tobyp/kthw/schematics/kthw_memory.sch

## KiCad design schematics/kthw_memory.sch (2019-12-05)

Schematic: kthw_memory.sch

Parts:
AFF5, AFF6, AFF7, AFF8, AFF9: LTS-6980HR
D43, D44, D45, D46, D47, D52: LED
D48, D49, D50, D51: 1N4148; D_DO-35_SOD27_Horizontal_RM10
R58, R59, R60, R61, R62, R63, R64, R65, R66, R67, R68, R69, R70, R71, R72, R73, R74, R75, R76, R77, R78, R79, R80, R81, R82, R83, R84, R85, R86, R87, R88, R89, R90, R91, R92, R93, R94, R95, R96, R97, R98, R99, R100, R101, R102, R103: 1K
SW13, SW14, SW15, SW16: SW_Push
U12, U13, U14, U15, U16, U17, U18: 74HC595
