tobyp/kthw/schematics/kthw_morse.sch

## KiCad design schematics/kthw_morse.sch (2019-12-05)

Schematic: kthw_morse.sch

Parts:
AFF1, AFF2, AFF3, AFF4: LTS-6980HR
D32, D33: LED
R19, R20, R21, R22, R23, R24, R25, R26, R27, R28, R29, R30, R31, R32, R33, R34, R35, R36, R37, R38, R39, R40, R41, R42, R43, R44, R45, R46, R47, R48, R49, R50, R51, R52: 1K
RV2: POT
SW8: SW_Push
U7, U8, U9, U10: 74HC595
