tobyp/kthw/schematics/kthw_password.sch

## KiCad design schematics/kthw_password.sch (2019-12-05)

Schematic: kthw_password.sch

Parts:
D1, D2, D3, D4, D5: 1N4148; D_DO-35_SOD27_Horizontal_RM10
D6: LED
DS1: LCD16X2; WC1602A
R1: 1K
RV1: 100K
SW2, SW3, SW4, SW5, SW6: SW_Push
U2, U3: 74HC595
