tobyp/kthw/schematics/kthw_schematics.sch

## KiCad design schematics/kthw_schematics.sch (2019-12-05)

Schematic: kthw_schematics.sch

Parts:
J1, J2: CONN_02X25
SW1: SW_SPST
U1: 7805
