tobyp/kthw/schematics/kthw_simonsays.sch

## KiCad design schematics/kthw_simonsays.sch (2019-12-05)

Schematic: kthw_simonsays.sch

Parts:
D34, D36, D38, D40: 1N4148; D_DO-35_SOD27_Horizontal_RM10
D35: LED_YL
D37: LED_RD
D39: LED_BL
D41: LED_GR
D42: LED
R53, R54, R55, R56, R57: 1K
SW9, SW10, SW11, SW12: SW_Push
U11: 74HC595
