tobyp/kthw/schematics/kthw_timer.sch

## KiCad design schematics/kthw_timer.sch (2019-12-05)

Schematic: kthw_timer.sch

Parts:
AFF10, AFF11, AFF12, AFF13: LTS-6980HR
D53, D54, D55: LED
D56, D57, D58, D59, D60, D61, D62, D63, D64, D65, D66, D67, D68, D69, D70, D71: 1N4148; D_DO-35_SOD27_Horizontal_RM10
J5: CONN_01X04
R104, R105, R106, R107, R108, R109, R110, R111, R112, R113, R114, R115, R116, R117, R118, R119, R120, R121, R122, R123, R124, R125, R126, R127, R128, R129, R130, R131, R132, R133, R134, R135, R136, R137, R138: 1K
SW17, SW18: SW_DIP_x08
U19, U20, U21, U22, U23, U24, U25: 74HC595
