tobyp/kthw/schematics/kthw_wires.sch

## KiCad design schematics/kthw_wires.sch (2019-12-05)

Schematic: kthw_wires.sch

Parts:
D7, D8, D9, D10, D11, D12, D13, D14: 1N4148; D_DO-35_SOD27_Horizontal_RM10
D15, D16, D17, D18, D19, D20, D21, D22, D23, D24, D25, D26, D27, D28, D29, D30, D31: LED
J3, J4: CONN_01X15
R2, R3, R4, R5, R6, R7, R8, R9, R10, R11, R12, R13, R14, R15, R16, R17, R18: 1K
SW7: SW_Push
U4, U5, U6: 74HC595
