tobyp/kthw/password.c

/* KTHW - Hardware Clone of Keep Talking and Nobody Explodes
Copyright (C) 2017 Toby P., Thomas H.
Copyright (C) 2019 Toby P.

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
You should have received a copy of the GNU General Public License
along with this program.  If not, see <http://www.gnu.org/licenses/>. */

#include "password.h"

#include <stdlib.h>

/* The password module has 5 cylinder columns of 6 letters each, which can be
spun to spell exactly one word from the a pre-defined list. To disable the
module, you must find that exact word, select it, and press the submit
button. */

struct word {
	char chars[6];
};

// impossibles[N] == the letters that can never appear in column N.
struct slot_impossible {
	unsigned char count;
	char letters[25];  // if all 26 were impossible, the puzzle would be unsolvable!
};

#include "password.words.generated.c"

#define BTN_RIGHT 0x1
#define BTN_LEFT 0x2
#define BTN_DOWN 0x4
#define BTN_UP 0x8
#define BTN_SUBMIT 0x10

static void populate_cylinders(struct password * password) {
	/* possibilities[word] tracks whether that word is possible, per column, as a bitmask.
	E.g. 0x1f means it is possible in every column and thus totally possible. */
	uint8_t possibilities[sizeof(words)/sizeof(struct word)];
	for (uint8_t i=0; i<sizeof(possibilities); ++i) {
		possibilities[i] = 0;
	}

	password->letters[0][0] = password->word->chars[0];
	password->letters[1][0] = password->word->chars[1];
	password->letters[2][0] = password->word->chars[2];
	password->letters[3][0] = password->word->chars[3];
	password->letters[4][0] = password->word->chars[4];

	uint32_t has_letter[5] = {
		1 << (password->letters[0][0] - 'A'),
		1 << (password->letters[1][0] - 'A'),
		1 << (password->letters[2][0] - 'A'),
		1 << (password->letters[3][0] - 'A'),
		1 << (password->letters[4][0] - 'A'),
	};

	for (uint8_t col=0; col<5; ++col) {
		for (uint8_t row=0; row<6; ++row) {
			if (row != 0) {  // row 0 already contains the password letter, don't change that
				/* generate a new letter for that column. */
				uint8_t letter = rnd_range(0, 26);
				while (has_letter[col] & (1 << letter)) {
					letter = (letter + 1) % 26;
				}
				password->letters[col][row] = letter + 'A';
				has_letter[col] |= (1 << letter);
			}
			for (uint8_t word=0; word<sizeof(possibilities); ++word) {
				if (words[word].chars[col] == password->letters[col][row]) {
					possibilities[word] |= (1 << col);
				}
			}
		}
	}

	for (uint8_t word=0; word<sizeof(possibilities); ++word) {
		if (&words[word] == password->word) continue;  // don't touch the password
		if (possibilities[word] == 0x1f) { //this word is possible but shouldn't be -- block it!
			/* select a random column to block the word on. */
			uint8_t col = rnd_range(0, 5);
			while (password->word->chars[col] == words[word].chars[col]) { //do not change a row where password == blockword
				col = (col + 1) % 5;
			}
			/* find the letter that makes the word possible */
			uint8_t row = 0;
			while (words[word].chars[col] != password->letters[col][row]) {
				++row;
			}
			/* Chose a replacement that never appears in that column, but also isn't a duplicate */
			uint8_t replacement = rnd_range(0, impossibles[col].count);
			while (has_letter[col] & (1 << impossibles[col].letters[replacement])) {
				replacement = (replacement + 1) % impossibles[col].count;
			}

			password->letters[col][row] = impossibles[col].letters[replacement];
		}
	}
}

void password_prepare_tick(struct bomb * bomb, struct module * module) {
	struct password * password = (struct password *)module;
	switch (password->ticks) {
	//init
	case 0:
		password->word = &words[rnd_range(0, sizeof(words)/sizeof(struct word))];
		printf("[%s] word=\"%s\"\n", module->name, password->word->chars);

		populate_cylinders(password);

		/* "Spin" the cylinders. Are you feeling lucky, punk? */
		password->selections[0] = rnd_range(0, 6);
		password->selections[1] = rnd_range(0, 6);
		password->selections[2] = rnd_range(0, 6);
		password->selections[3] = rnd_range(0, 6);
		password->selections[4] = rnd_range(0, 6);

		password->lcd->mode = LCD_CMD;
		password->lcd->cmd = 0x0c;
		break;
	case 1:
		password->lcd->mode = LCD_CMD;
		password->lcd->cmd = 0x38;
		break;
	case 2:
		password->lcd->mode = LCD_CMD;
		password->lcd->cmd = 0x06;
		break;
	case 3:
		password->lcd->mode = LCD_CMD;
		password->lcd->cmd = 0x01;
		break;
	//password
	case 4:
		password->lcd->mode = LCD_CMD;
		password->lcd->cmd = LCD_CMD_CURSOR(0, 1);
		break;
	case 5:
		password->lcd->mode = LCD_DATA;
		password->lcd->cmd = password->letters[0][password->selections[0]];
		break;
	case 6:
		password->lcd->mode = LCD_CMD;
		password->lcd->cmd = LCD_CMD_CURSOR(0, 4);
		break;
	case 7:
		password->lcd->mode = LCD_DATA;
		password->lcd->cmd = password->letters[1][password->selections[1]];
		break;
	case 8:
		password->lcd->mode = LCD_CMD;
		password->lcd->cmd = LCD_CMD_CURSOR(0, 7);
		break;
	case 9:
		password->lcd->mode = LCD_DATA;
		password->lcd->cmd = password->letters[2][password->selections[2]];
		break;
	case 10:
		password->lcd->mode = LCD_CMD;
		password->lcd->cmd = LCD_CMD_CURSOR(0, 10);
		break;
	case 11:
		password->lcd->mode = LCD_DATA;
		password->lcd->cmd = password->letters[3][password->selections[3]];
		break;
	case 12:
		password->lcd->mode = LCD_CMD;
		password->lcd->cmd = LCD_CMD_CURSOR(0, 13);
		break;
	case 13:
		password->lcd->mode = LCD_DATA;
		password->lcd->cmd = password->letters[4][password->selections[4]];
		break;
	case 14:
		password->lcd->mode = LCD_CMD;
		password->lcd->cmd = LCD_CMD_CURSOR(1, 1);
		break;
	case 15:
		password->lcd->mode = LCD_DATA;
		password->lcd->cmd = '^';
		break;
	default:
		password->ticks = 0;
		password->ser->value = 1;
		module->flags |= MF_READY;
		return;
	}
	password->ticks++;
}

void password_tick(struct bomb * bomb, struct module * module) {
	struct password * password = (struct password *)module;
	uint8_t pos = password->pos;
	uint8_t sel = password->selections[pos];

	uint32_t button_index = password->ticks;
	uint8_t button_mask = 1 << button_index;
	uint8_t button_value = gpio_get(password->in) ? button_mask : 0;
	if ((password->cache & button_mask) != button_value) {
		password->cache = (password->cache & ~button_mask) | button_value;
		if (button_value) {
			if (button_value == BTN_LEFT) {
				if (password->pos > 0) password->pos--;
			}
			else if (button_value == BTN_RIGHT) {
				if (password->pos < 4) password->pos++;
			}
			else if (button_value == BTN_UP) {
				sel = (sel + 5) % 6; //equivalent to -1 without the underflow (which should be harmless but makes me queasy)
			}
			else if (button_value == BTN_DOWN) {
				sel = (sel + 1) % 6;
			}
			else if (button_value == BTN_SUBMIT) {
				for (uint8_t i=0; i<6; ++i) {
					if (password->letters[i][password->selections[i]] != password->word->chars[i]) {
						strike(bomb, module);
						return;
					}
				}
				module->flags |= MF_COMPLETE;
				return;
			}
		}
	}

	if (password->pos != pos) {
		sel = password->selections[pos];
		password->lcd_cache[0].mode = LCD_CMD;
		password->lcd_cache[0].cmd = LCD_CMD_CURSOR(1, 1 + 3*pos);
		password->lcd_cache[1].mode = LCD_DATA;
		password->lcd_cache[1].cmd = ' ';
		password->lcd_cache[2].mode = LCD_CMD;
		password->lcd_cache[2].cmd = LCD_CMD_CURSOR(1, 1 + 3*password->pos);
		password->lcd_cache[3].mode = LCD_DATA;
		password->lcd_cache[3].cmd = '^';
	}

	if (password->selections[pos] != sel) {
		password->selections[pos] = sel;
		password->lcd_cache[4].mode = LCD_CMD;
		password->lcd_cache[4].cmd = LCD_CMD_CURSOR(0, 1 + 3*pos);
		password->lcd_cache[5].mode = LCD_DATA;
		password->lcd_cache[5].cmd = password->letters[pos][sel];
	}

	password->ticks = (password->ticks + 1) % 5;
	password->ser->value = 1 << password->ticks;

	//apply next LCD command
	for (uint8_t i=0; i<6; ++i) {
		if (password->lcd_cache[i].mode != LCD_NONE) {
			password->lcd->mode = password->lcd_cache[i].mode;
			password->lcd->cmd = password->lcd_cache[i].cmd;
			password->lcd_cache[i].mode = LCD_NONE;
			break;
		}
	}
}

void password_reset(struct bomb * bomb, struct module * module) {
	struct password * password = (struct password *)module;

	password->lcd->mode = LCD_CMD;
	password->lcd->cmd = 0x01;
}
